kildom/home-controller/bootloader/router/Core/Src/main.c

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
/* Includes ------------------------------------------------------------------*/
#include "main.h"


CRC_HandleTypeDef hcrc;

void SystemClock_Config(void);
static void MX_GPIO_Init(void);
static void MX_USART1_UART_Init(void);
static void MX_USART2_UART_Init(void);
static void MX_CRC_Init(void);
/* USER CODE BEGIN 0 */

HAL_StatusTypeDef HAL_InitTick(uint32_t TickPriority)
{
  return HAL_OK;
}

/* USER CODE END 0 */

/**
  * @brief  The application entry point.
  * @retval int
  */
int main(void)
{

  /* USER CODE BEGIN 1 */

  __disable_irq();

  /* USER CODE END 1 */

  /* MCU Configuration--------------------------------------------------------*/

  /* Reset of all peripherals, Initializes the Flash interface and the Systick. */
  HAL_Init();

  /* Configure the system clock */
  SystemClock_Config();

  /* Initialize all configured peripherals */
  MX_GPIO_Init();
  MX_USART1_UART_Init();
  MX_USART2_UART_Init();
  MX_CRC_Init();
  /* USER CODE BEGIN 2 */

  __disable_irq();

  /* USER CODE END 2 */

  /* Infinite loop */
  /* USER CODE BEGIN WHILE */
  while (1)
  {
    void uartPoll(USART_TypeDef *uart0, USART_TypeDef *uart1, USART_TypeDef *uart2, USART_TypeDef *uart3);
    uartPoll(USART1, USART2, NULL, NULL);
    /* USER CODE END WHILE */

    /* USER CODE BEGIN 3 */
  }
  /* USER CODE END 3 */
}

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
